jKill709/VR-Collision-Avoidance-Sensor/arduino_version/hardware/Circut_Map.png

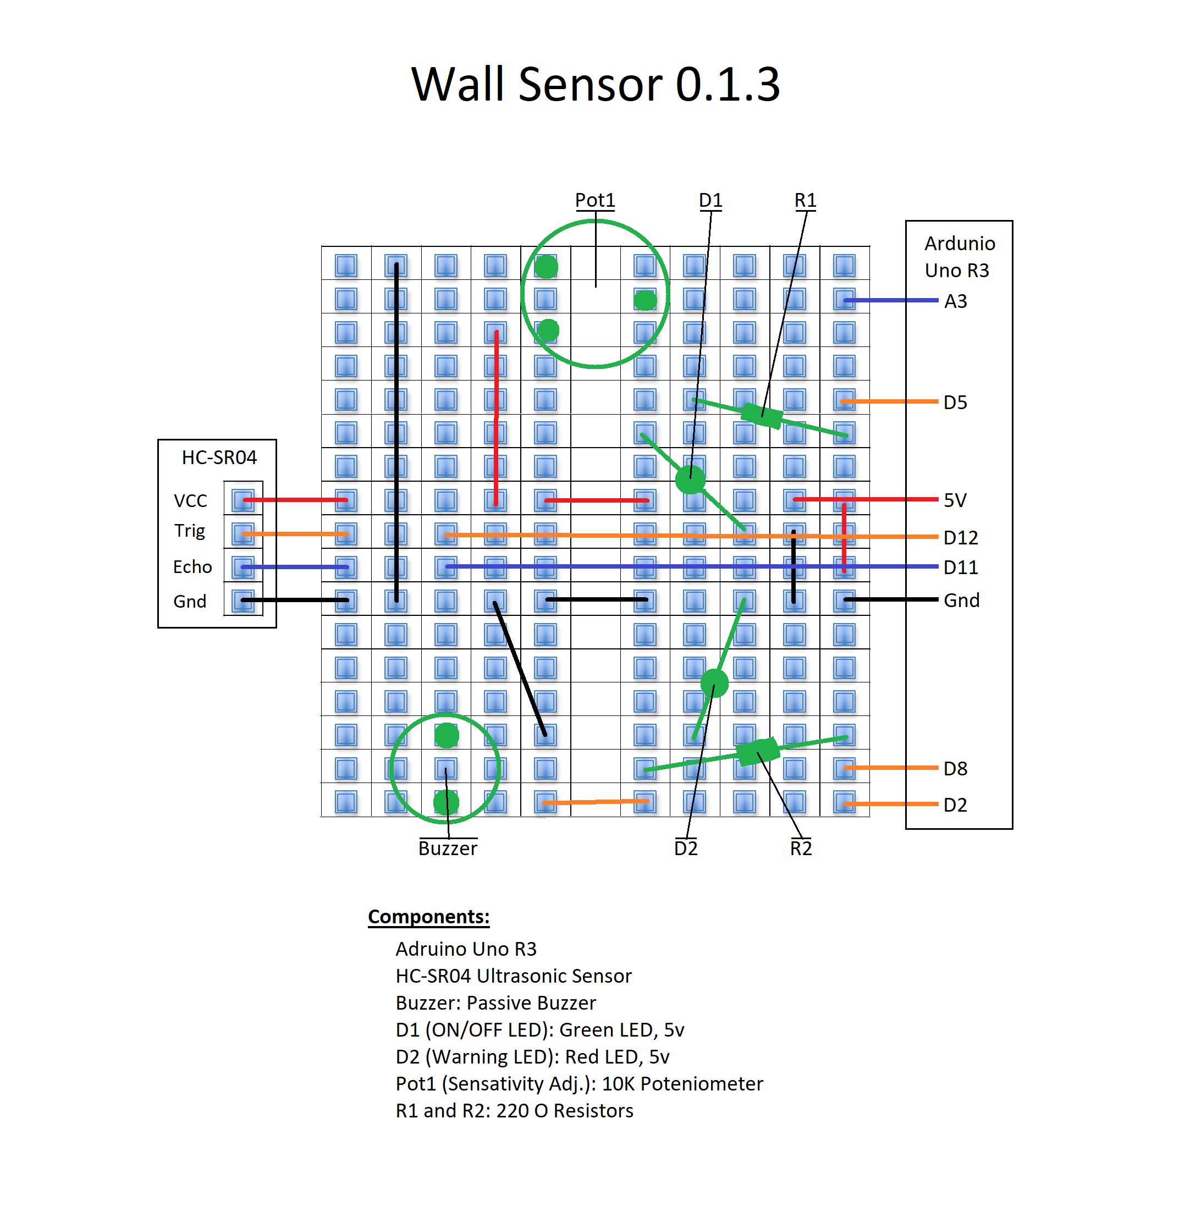
arduino_version/hardware/Circut_Map.png
