jKill709/VR-Collision-Avoidance-Sensor/arduino_version/images/arduino-uno-r3.jpg

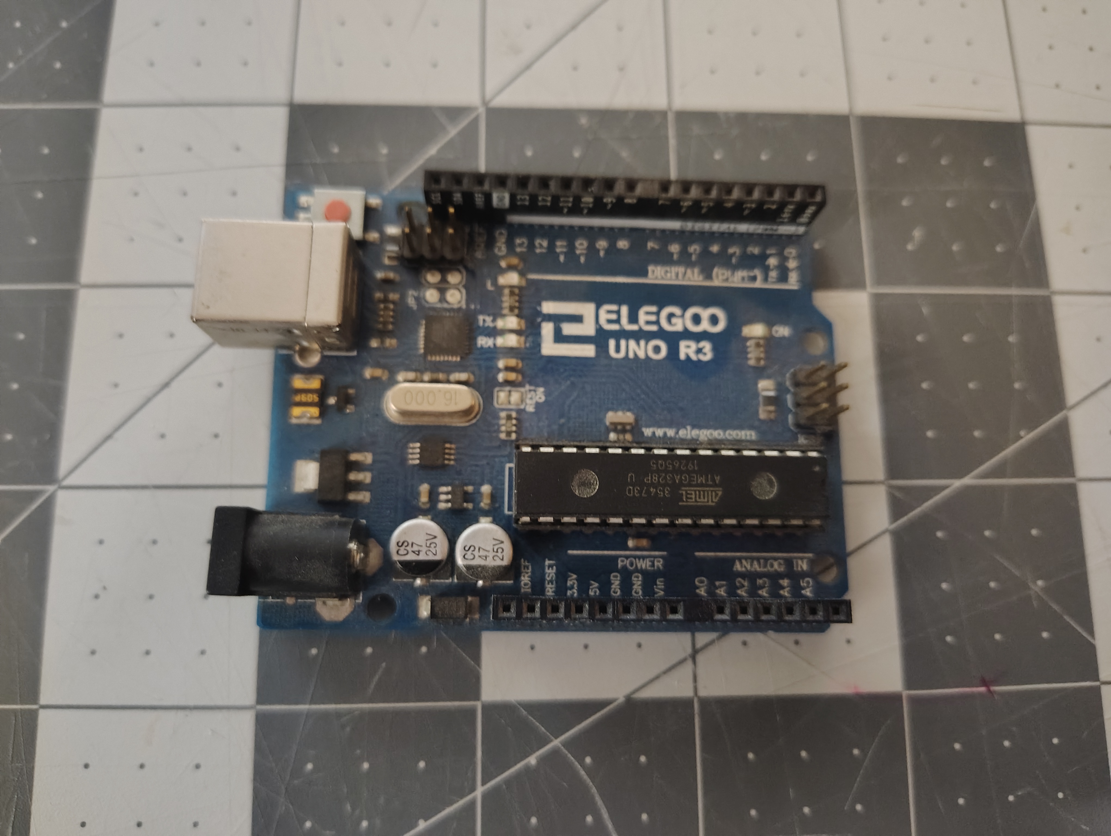
arduino_version/images/arduino-uno-r3.jpg
