jKill709/VR-Collision-Avoidance-Sensor/pcb_version/images/board-top.png

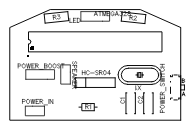
pcb_version/images/board-top.png
