jKill709/VR-Collision-Avoidance-Sensor/pcb_version/images/led-magnified.jpg

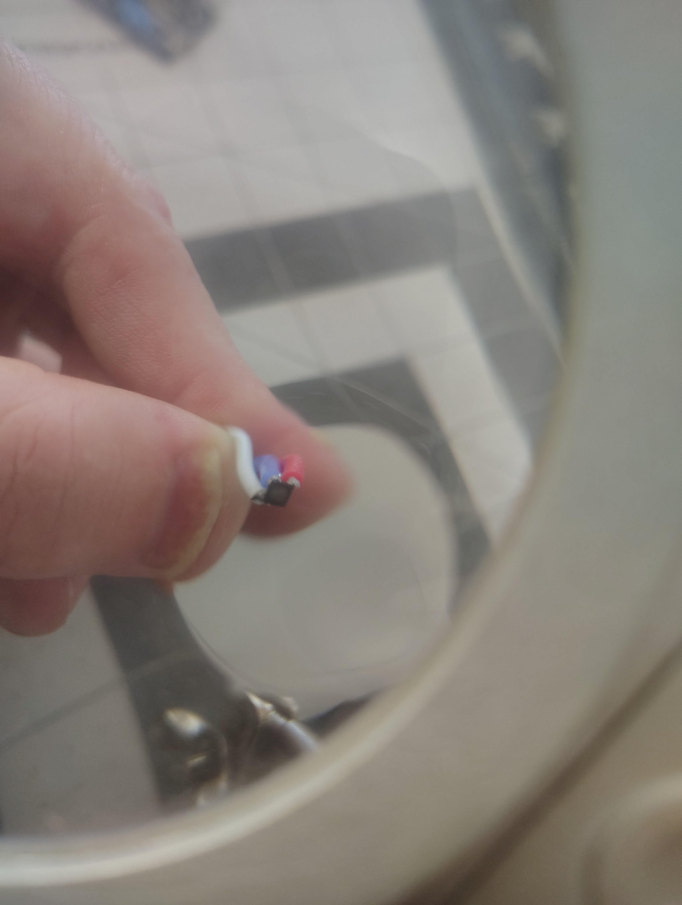
pcb_version/images/led-magnified.jpg
