jKill709/VR-Collision-Avoidance-Sensor/atmega_breadboard_version/images/assembled-rear.jpg

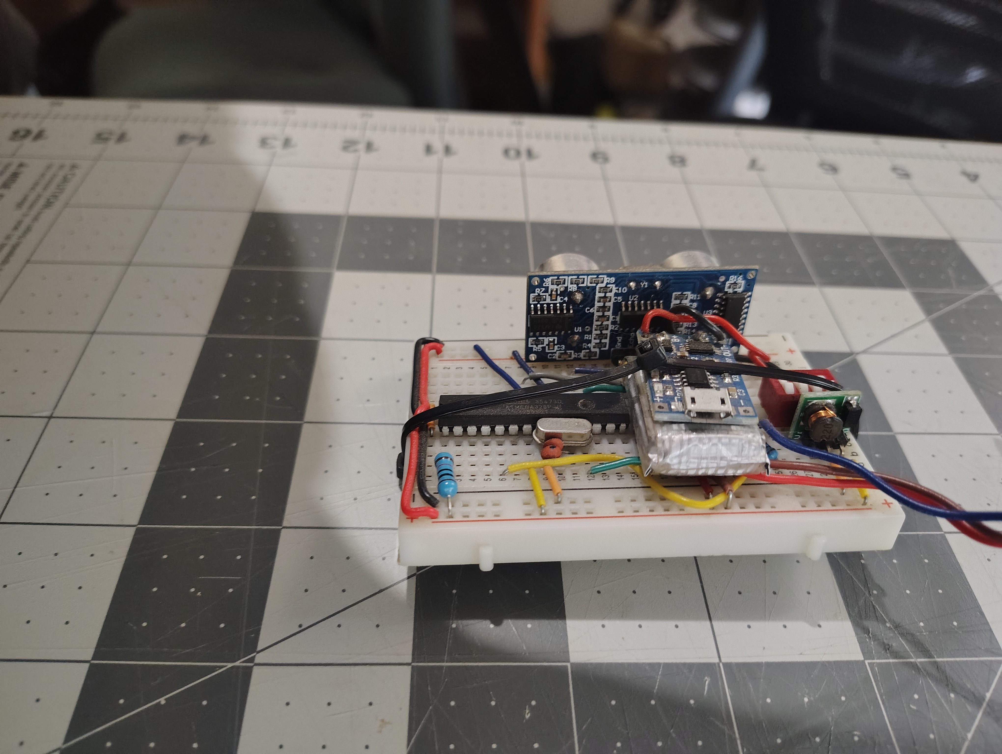
atmega_breadboard_version/images/assembled-rear.jpg
