jKill709/VR-Collision-Avoidance-Sensor/pcb_version/images/installed-1.jpg

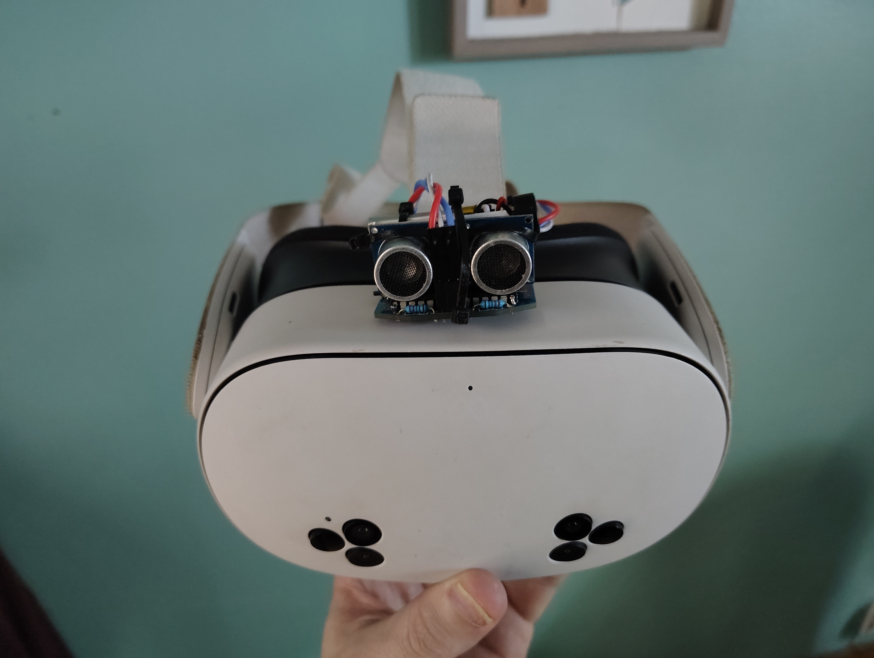
pcb_version/images/installed-1.jpg
