jKill709/VR-Collision-Avoidance-Sensor/pcb_version/images/power-subassembly.jpg

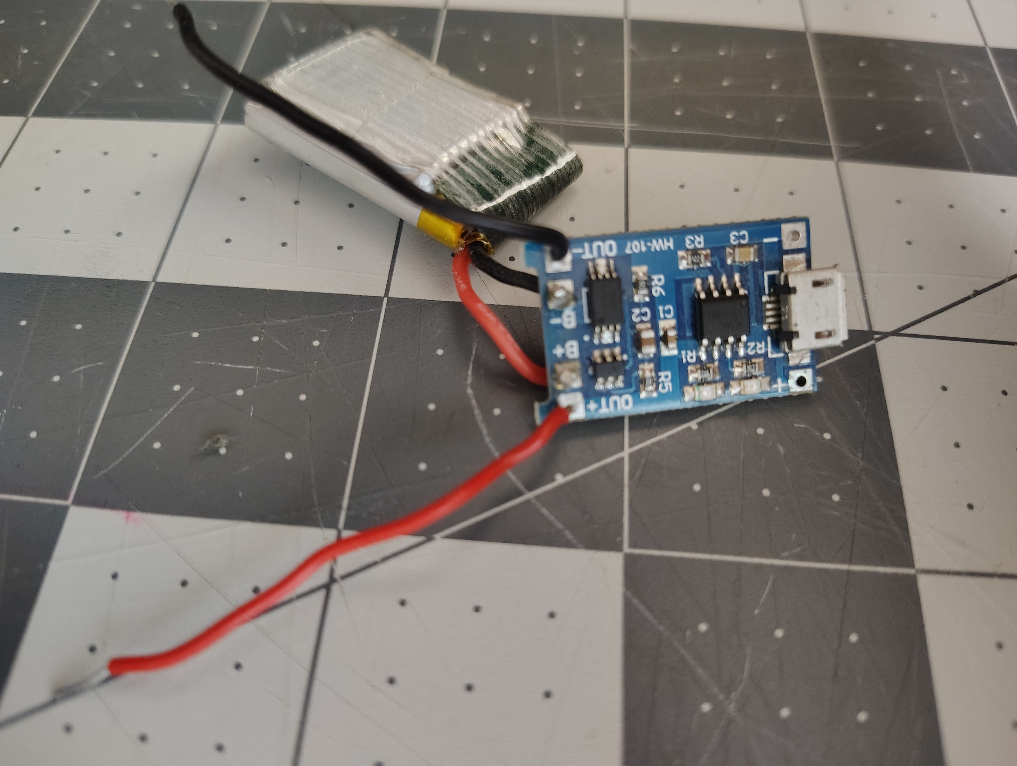
pcb_version/images/power-subassembly.jpg
