jKill709/VR-Collision-Avoidance-Sensor/pcb_version/images/speaker-subassembly-side.jpg

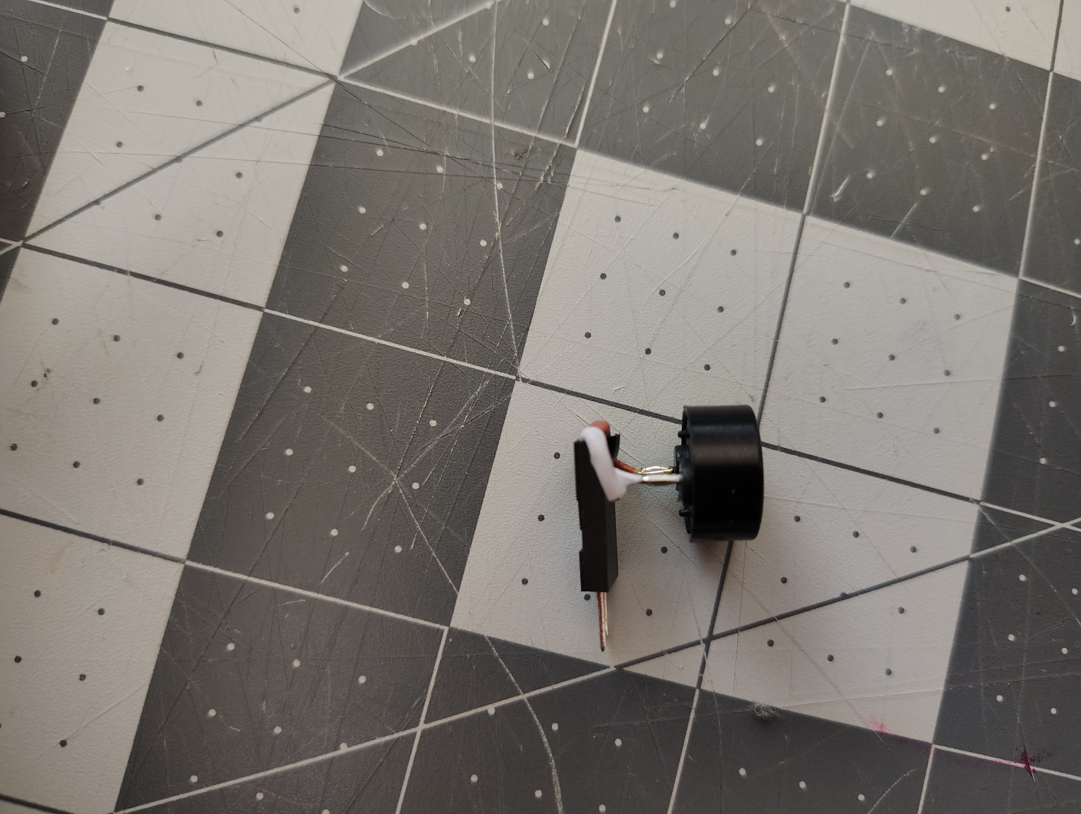
pcb_version/images/speaker-subassembly-side.jpg
