jKill709/VR-Collision-Avoidance-Sensor/pcb_version/images/speaker-subassembly-top.jpg

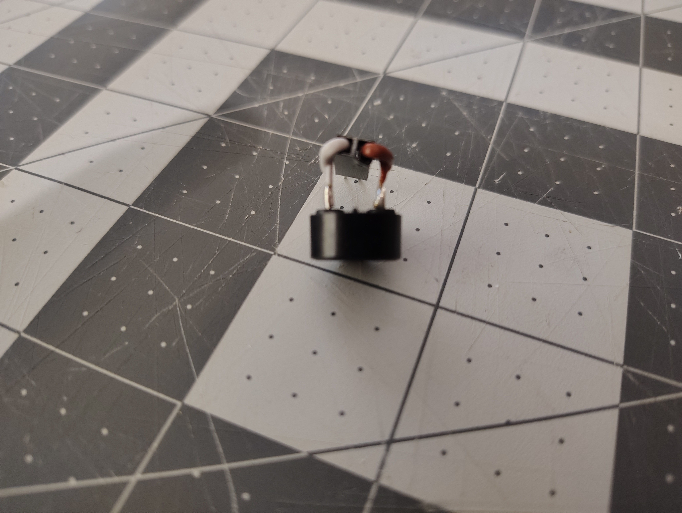
pcb_version/images/speaker-subassembly-top.jpg
